karol-design/BEng_project/board-design/FMP_Proto_2.0/Project Outputs for MFMS_Node/Proto2.0_3D.png

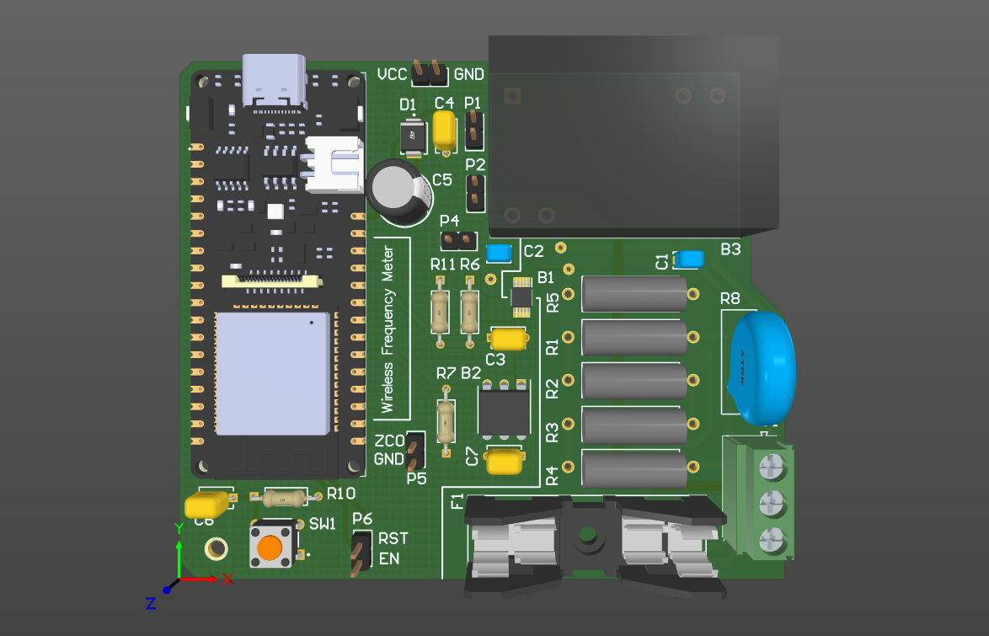
board-design/FMP_Proto_2.0/Project Outputs for MFMS_Node/Proto2.0_3D.png
