karol-design/BEng_project/board-design/FMP_Proto_4.0/Project Outputs for FMP_Proto_4.0/Proto4.0_SCH.png

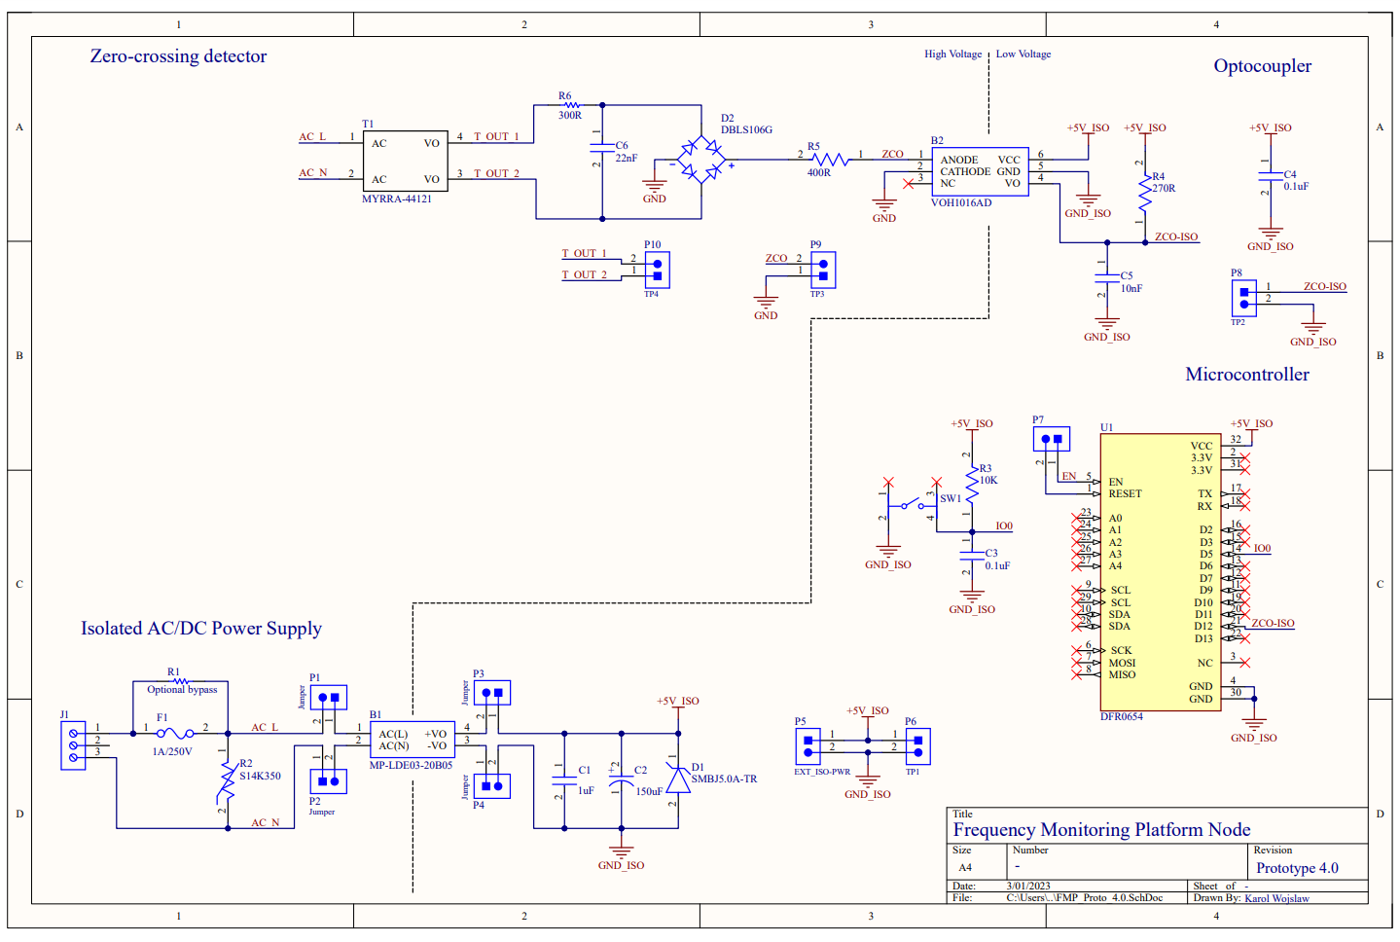
board-design/FMP_Proto_4.0/Project Outputs for FMP_Proto_4.0/Proto4.0_SCH.png
